CIMIL/musmet-bridge/docs/IMG_1561.jpg

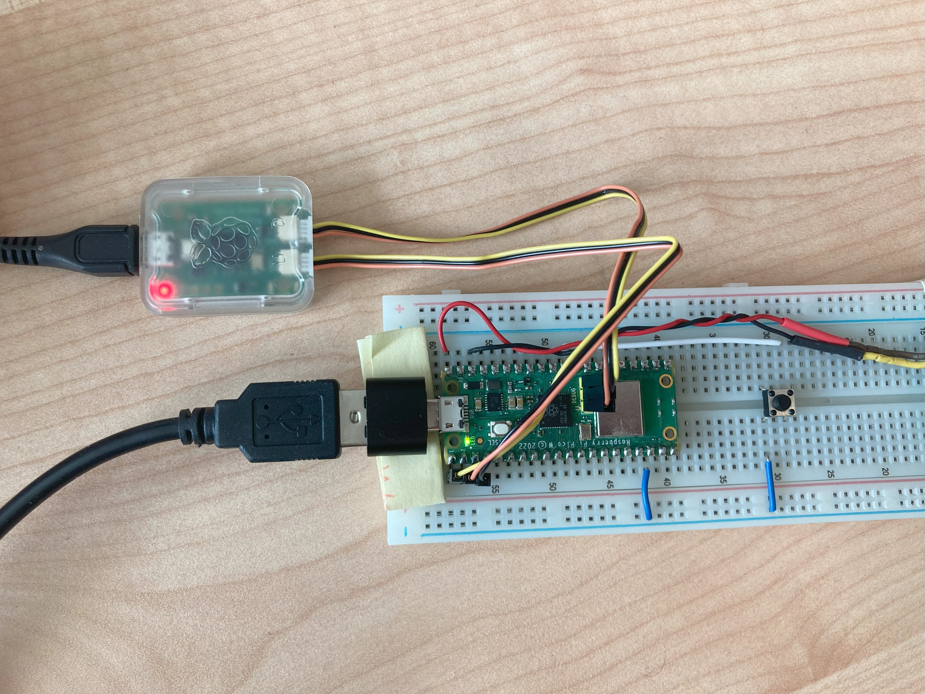
docs/IMG_1561.jpg
