CIMIL/musmet-bridge/docs/IMG_1562.jpg

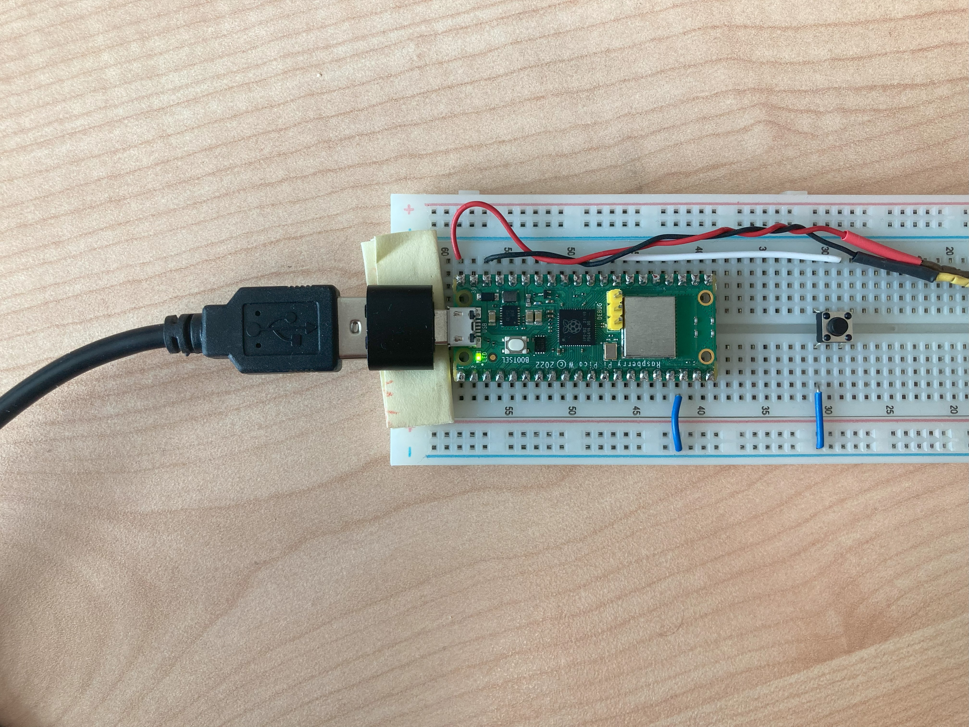
docs/IMG_1562.jpg
