CIMIL/musmet-bridge/docs/IMG_1563.jpg

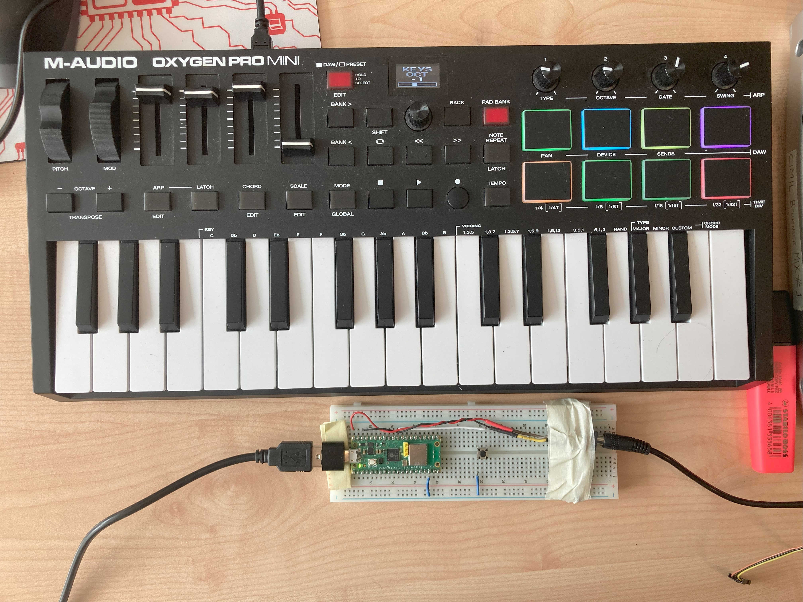
docs/IMG_1563.jpg
