CIMIL/musmet-bridge/tests/test_OSC/test_Udp/test_Udp.ino

/*
  UDPSendReceive.pde:
  This sketch receives UDP message strings, prints them to the serial port
  and sends an "acknowledge" string back to the sender

  A Processing sketch is included at the end of file that can be used to send
  and received messages for testing with a computer.

  created 21 Aug 2010
  by Michael Margolis

  This code is in the public domain.

  adapted from Ethernet library examples
*/


#include <WiFi.h>
#include <WiFiUdp.h>

#ifndef STASSID
#define STASSID "AndroidAP46E6"
#define STAPSK "gregorio"
#endif

unsigned int localPort = 8888;  // local port to listen on

// buffers for receiving and sending data
char packetBuffer[UDP_TX_PACKET_MAX_SIZE + 1];  // buffer to hold incoming packet,
char ReplyBuffer[] = "acknowledged\r\n";        // a string to send back

WiFiUDP Udp;

void setup() {
  Serial.begin(115200);
  WiFi.begin(STASSID, STAPSK);
  while (WiFi.status() != WL_CONNECTED) {
    Serial.print('.');
    delay(500);
  }
  Serial.print("Connected! IP address: ");
  Serial.println(WiFi.localIP());
  Serial.printf("UDP server on port %d\n", localPort);
  Udp.begin(localPort);
}

void loop() {
  // if there's data available, read a packet
  int packetSize = Udp.parsePacket();
  if (packetSize) {
    Serial.printf("Received packet of size %d from %s:%d\n    (to %s:%d)\n", packetSize, Udp.remoteIP().toString().c_str(), Udp.remotePort(), Udp.destinationIP().toString().c_str(), Udp.localPort());

    // read the packet into packetBufffer
    int n = Udp.read(packetBuffer, UDP_TX_PACKET_MAX_SIZE);
    packetBuffer[n] = 0;
    Serial.println("Contents:");
    Serial.println(packetBuffer);

    // send a reply, to the IP address and port that sent us the packet we received
    Udp.beginPacket(Udp.remoteIP(), Udp.remotePort());
    Udp.write(ReplyBuffer);
    Udp.endPacket();
  }
}

/*
  test (shell/netcat):
  --------------------
    nc -u 192.168.pico.address 8888
*/
